3d-paws/3D-PAWS-Particle-SurgeAndWindGauge/src/output.cpp

/*
 * ======================================================================================================================
 *  output.cpp - OLED and Serial Console Fuctions
 * ======================================================================================================================
 */
#include "include/ssbits.h"
#include "include/support.h"
#include "include/main.h"
#include "include/output.h"

/*
 * ======================================================================================================================
 * Variables and Data Structures
 * =======================================================================================================================
 */

/*
 * ======================================================================================================================
 *  Serial Console Enable
 * ======================================================================================================================
 */
int SCE_PIN = D8;
bool SerialConsoleEnabled = false;  // Variable for serial monitor control

bool DisplayEnabled = true;
int  oled_type = 0;
char oled_lines[8][23];
Adafruit_SSD1306 display32(SCREEN_WIDTH, 32, &Wire, OLED_RESET);
Adafruit_SSD1306 display64(SCREEN_WIDTH, 64, &Wire, OLED_RESET);

/*
 * ======================================================================================================================
 * Fuction Definations
 * =======================================================================================================================
 */

/*
 * ======================================================================================================================
 * OLED_sleepDisplay()
 * ======================================================================================================================
 */
void OLED_sleepDisplay() {
  if (DisplayEnabled) {
    if (OLED32) {
      display32.ssd1306_command(SSD1306_DISPLAYOFF);
    }
    else {
      display64.ssd1306_command(SSD1306_DISPLAYOFF);
    }
  }
}

/*
 * ======================================================================================================================
 * OLED_wakeDisplay()
 * ======================================================================================================================
 */
void OLED_wakeDisplay() {
  if (DisplayEnabled) {
    if (OLED32) {
      display32.ssd1306_command(SSD1306_DISPLAYON);
    }
    else {
      display64.ssd1306_command(SSD1306_DISPLAYON);
    }
  }
}

/*
 * ======================================================================================================================
 * OLED_spin() 
 * ======================================================================================================================
 */
void OLED_spin() {
  static int spin=0;
    
  if (DisplayEnabled) {
    if (OLED32) {
      display32.setTextColor(WHITE, BLACK); // Draw 'inverse' text
      display32.setCursor(120,24);
      display32.print(" ");
      display32.setCursor(120,24); 
    }
    else {
      display64.setTextColor(WHITE, BLACK); // Draw 'inverse' text
      display64.setCursor(120,24);
      display64.print(" ");
      display64.setCursor(120,24);
      display64.setCursor(120,56);
      display64.print(" ");
      display64.setCursor(120,56);       
    } 
    switch (spin++) {
      case 0 : msgp = (char *) "|"; break;
      case 1 : msgp = (char *) "/"; break;
      case 2 : msgp = (char *) "-"; break;
      case 3 : msgp = (char *) "\\"; break;
    }
    if (OLED32) {
      display32.print(msgp);
      display32.display();
    }
    else {
      display64.print(msgp);
      display64.display();
    }
    spin %= 4;
  }
}


/*
 * ======================================================================================================================
 * OLED_update() -- Output oled in memory map to display
 * ======================================================================================================================
 */
void OLED_update() {  
  if (DisplayEnabled) {
    if (OLED32) {
      display32.clearDisplay();
      display32.setCursor(0,0);             // Start at top-left corner
      display32.print(oled_lines [0]);
      display32.setCursor(0,8);
      display32.print(oled_lines [1]);
      display32.setCursor(0,16);
      display32.print(oled_lines [2]);
      display32.setCursor(0,24);  
      display32.print(oled_lines [3]);
      display32.display();
    }
    else {
      display64.clearDisplay();
      display64.setCursor(0,0);             // Start at top-left corner
      display64.print(oled_lines [0]);
      display64.setCursor(0,8);
      display64.print(oled_lines [1]);
      display64.setCursor(0,16);
      display64.print(oled_lines [2]);
      display64.setCursor(0,24);  
      display64.print(oled_lines [3]);
      display64.setCursor(0,32);  
      display64.print(oled_lines [4]);
      display64.setCursor(0,40);  
      display64.print(oled_lines [5]);
      display64.setCursor(0,48);  
      display64.print(oled_lines [6]);
      display64.setCursor(0,56);  
      display64.print(oled_lines [7]);
      display64.display();
     
    }
  }
}

/*
 * ======================================================================================================================
 * OLED_write() 
 * ======================================================================================================================
 */
void OLED_write(const char *str) {
  int c, len, bottom_line = 3;
  
  if (DisplayEnabled) {
    // move lines up
    for (c=0; c<=21; c++) {
      oled_lines [0][c] = oled_lines [1][c];
      oled_lines [1][c] = oled_lines [2][c];
      oled_lines [2][c] = oled_lines [3][c];
      if (OLED64) {
        oled_lines [3][c] = oled_lines [4][c];
        oled_lines [4][c] = oled_lines [5][c];
        oled_lines [5][c] = oled_lines [6][c];  
        oled_lines [6][c] = oled_lines [7][c];  
        bottom_line = 7;          
      }
    }

    // check length on new output line string
    len = strlen (str);
    if (len>21) {
      len = 21;
    }
    for (c=0; c<=len; c++) {
      oled_lines [bottom_line][c] = *(str+c);
    }

    // Adding Padding
    for (;c<=21; c++) {
      oled_lines [bottom_line][c] = ' ';
    }
    oled_lines [bottom_line][22] = (char) NULL;
    
    OLED_update();
  }
}

/*
 * ======================================================================================================================
 * OLED_write_noscroll() -- keep lines 1-3 and output on line 4
 * ======================================================================================================================
 */
void OLED_write_noscroll(const char *str) {
  int c, len, bottom_line = 3;

  if (OLED64) {
    bottom_line = 7;
  }

  if (DisplayEnabled) {
    len = strlen (str);
    if (len>21) {
      len = 21;
    }
    
    for (c=0; c<=len; c++) {
      oled_lines [bottom_line][c] = *(str+c);
    }

    // Adding Padding
    for (;c<=21; c++) {
      oled_lines [bottom_line][c] = ' ';
    }
    oled_lines [bottom_line][22] = (char) NULL;
    
    OLED_update();
  }
}

/*
 * ======================================================================================================================
 * Serial_write() 
 * ======================================================================================================================
 */
void Serial_write(const char *str) {
  if (SerialConsoleEnabled) {
    Serial.println(str);
  }
}

/*
 * ======================================================================================================================
 * Serial_writeln() 
 * ======================================================================================================================
 */
void Serial_writeln(const char *str) {
  if (SerialConsoleEnabled) {
    Serial.println(str);
    Serial.flush();
  }
}

/*
 * ======================================================================================================================
 * Output()
 * ======================================================================================================================
 */
void Output(const char *str) {
  OLED_write(str);
  Serial_write(str);
}

/*
 * ======================================================================================================================
 * OutputNS() - Output with no scroll on oled
 * ======================================================================================================================
 */
void OutputNS(const char *str) {
  OLED_write_noscroll(str);
  Serial_write(str);
}

/*
 * ======================================================================================================================
 * OLED_initialize() -- Initialize oled if enabled
 * ======================================================================================================================
 */
void OLED_initialize() {
  if (DisplayEnabled) {
    if (I2C_Device_Exist (OLED32_I2C_ADDRESS)) {
      oled_type = OLED32_I2C_ADDRESS;
      display32.begin(SSD1306_SWITCHCAPVCC, OLED32_I2C_ADDRESS);
      display32.clearDisplay();
      display32.setTextSize(1); // Draw 2X-scale text
      display32.setTextColor(WHITE);
      display32.setCursor(0, 0);
      for (int r=0; r<4; r++) {
        oled_lines[r][0]=0;
      }
      OLED_write("OLED32:OK");
    }
    else if (I2C_Device_Exist (OLED64_I2C_ADDRESS)) {
      oled_type = OLED64_I2C_ADDRESS;
      display64.begin(SSD1306_SWITCHCAPVCC, OLED64_I2C_ADDRESS);
      display64.clearDisplay();
      display64.setTextSize(1); // Draw 2X-scale text
      display64.setTextColor(WHITE);
      display64.setCursor(0, 0);
      for (int r=0; r<8; r++) {
        oled_lines[r][0]=0;
      }
      OLED_write("OLED64:OK");
    }
    else {
      DisplayEnabled = false;
    }
  }
}

/*
 * ======================================================================================================================
 * Serial_Initialize() -
 * ======================================================================================================================
 */
void Serial_Initialize() {
  // serial console enable pin
  pinMode(SCE_PIN, INPUT_PULLUP);   // Internal pullup resistor biases the pin to supply voltage.
                                    // If jumper set to ground, we enable serial console (low = enable)
  if (digitalRead(SCE_PIN) == LOW) {
    SerialConsoleEnabled = true;
  }

  // There are libraries that print to Serial Console so we need to initialize no mater what the jumper is set to.
  Serial.begin(9600);
  delay(1000); // prevents usb driver crash on startup, do not omit this

  if (SerialConsoleEnabled) {
    // Wait for serial port to be available
    if (!Serial.isConnected()) {
      OLED_write("Wait4 Serial Console");
    }
    int countdown=60; // Wait N seconds for serial connection, then move on.
    while (!Serial.isConnected() && countdown) {
      HeartBeat(); // Provices 250ms delay
      Blink(1, 750);
      countdown--;
    }

    Serial_writeln(""); // Send carriage return and linefeed
    
    if (DisplayEnabled) {
      Serial_writeln ("OLED:Enabled");
    }
    else {
      Serial_writeln ("OLED:Disabled");
    }
    Output ("SC:Enabled");
  }
}

/*
 * ======================================================================================================================
 * Output_Initialize() -
 * ======================================================================================================================
 */
void Output_Initialize() {
  OLED_initialize();
  Output("SER:Init");
  Serial_Initialize();
  Output("SER:OK");
}
