3d-paws/3D-PAWS-Particle-SurgeAndWindGauge/src/info.cpp

/*
 * ======================================================================================================================
 *  info.cpp - Station Information Functions
 * ======================================================================================================================
 */
#include <Particle.h>
#include <SdFat.h>
#include <RTClib.h>

#include "include/ssbits.h"
#include "include/eeprom.h"
#include "include/cf.h"
#include "include/sensors_i2c_44_47.h"
#include "include/sensors.h"
#include "include/wrda.h"
#include "include/sdcard.h"
#include "include/output.h"
#include "include/support.h"
#include "include/time.h"
#include "include/ps.h"
#include "include/obs.h"
#include "include/main.h"
#include "include/info.h"

/*
 * ======================================================================================================================
 * INFO_Do() - Get and Send System Information to Particle Cloud
 * ======================================================================================================================
 */
bool INFO_Do() {
  char buf[256];
  const char *comma = "";
  time_t ts = Time.now();

  Output("INFO_DO()");

  SendSystemInformation = false;

  memset(buf, 0, sizeof(buf));        // holds string of found sensors 
  memset(msgbuf, 0, sizeof(msgbuf));  // hold the json formatted message we are building for sending.

  JSONBufferWriter writer(msgbuf, sizeof(msgbuf)-1);
  writer.beginObject();

  writer.name("devid").value(System.deviceID());
  writer.name("devos").value(System.version());
  writer.name("freemem").value(System.freeMemory());
  writer.name("uptime").value(System.uptime());

#if PLATFORM_ID == PLATFORM_ARGON
  writer.name("type").value("argon");
#endif
#if PLATFORM_ID == PLATFORM_BORON
  writer.name("board").value("boron");
#endif

  sprintf (Buffer32Bytes, "%d-%02d-%02dT%02d:%02d:%02d",
    Time.year(ts), Time.month(ts), Time.day(ts),
    Time.hour(ts), Time.minute(ts), Time.second(ts));
  writer.name("at").value(Buffer32Bytes);

  writer.name("ver").value(versioninfo);
  writer.name("hth").value((int) SystemStatusBits);

   // Reboot/Reset Reason and data
  sprintf (Buffer32Bytes,"%d-%d", (int) System.resetReason(), (int) System.resetReasonData());
  writer.name("rr").value(Buffer32Bytes);

  sprintf (Buffer32Bytes,"6m");
  writer.name("obsi").value(Buffer32Bytes);

  sprintf (Buffer32Bytes,"6m");
  writer.name("obsti").value(Buffer32Bytes);

  // Time 2 Next Transmit in Seconds
  // sprintf (Buffer32Bytes, "%ds", (int) ((obs_tx_interval * 60) - ((System.millis() - LastTransmitTime)/1000)));
  // writer.name("t2nt").value(Buffer32Bytes);

  // Daily Reboot Countdown Timer
  writer.name("drct").value(DailyRebootCountDownTimer);

  // Need 2 Send File
  if (SD.exists(SD_n2s_file)) {
    File fp = SD.open(SD_n2s_file, FILE_WRITE);
    if (fp) {
      writer.name("n2s").value(fp.size());
      fp.close();
    }
    else {
      writer.name("n2s").value(-1);
    }
  }
  else {
    writer.name("n2s").value("NF");
  }

#if PLATFORM_ID == PLATFORM_ARGON
  writer.name("ps").value((digitalRead(PWR)) ? "USB" : "BATTERY");
  writer.name("bv").value(analogRead(BATT) * 0.0011224); // Battery Voltage
  writer.name("bcs").value((digitalRead(PWR) && !digitalRead(CHG)) ? "CHARGING" : "!CHARGING"); // Battery Charger State
#endif

#if PLATFORM_ID == PLATFORM_BORON
  // Power Source
  const char *ps[] = {"UNKN", "VIN", "USB_HOST", "USB_ADAPTER", "USB_OTG", "BATTERY"};
  int sps = System.powerSource();
  if ((sps>=0) && (sps<=5)) {
    writer.name("ps").value(ps[sps]);
  }
  else {
    writer.name("ps").value(sps);
  }

  // Battery Charge State
  const char *bs[] = {"UNKN", "!CHARGING", "CHARGING", "CHARGED", "DISCHARGING", "FAULT", "MISSING"};
  int sbs = System.batteryState();
  if ((sbs>=0) && (sbs<=6)) {
    writer.name("bcs").value(bs[sbs]);     
  }
  else {
    writer.name("bcs").value(sbs);
  }
  writer.name("bpc").value(System.batteryCharge(), 1);   // Battery Percent Charge
#endif

#if PLATFORM_ID == PLATFORM_ARGON
  WiFiSignal sig = WiFi.RSSI();
  writer.name("wss").value(sig.getStrength(), 4);
  writer.name("wsq").value(sig.getQuality(), 4);
  byte mac[6];
  WiFi.macAddress(mac);
  sprintf (Buffer32Bytes, "%02x:%02x:%02x:%02x:%02x:%02x", mac[0], mac[1], mac[2], mac[3], mac[4], mac[5]);
  writer.name("mac").value(Buffer32Bytes);
  writer.name("ip").value(WiFi.localIP().toString().c_str());
  writer.name("mask").value(WiFi.subnetMask().toString().c_str());
  writer.name("gateway").value(WiFi.gatewayIP().toString().c_str());
  writer.name("dns").value(WiFi.dnsServerIP().toString().c_str());
  writer.name("dhcps").value(WiFi.dhcpServerIP().toString().c_str());
  writer.name("ssid").value(WiFi.SSID());
  WiFi.BSSID(mac);
  sprintf (Buffer32Bytes, "%02x:%02x:%02x:%02x:%02x:%02x", mac[0], mac[1], mac[2], mac[3], mac[4], mac[5]);
  writer.name("bssid").value(Buffer32Bytes);
#endif

#if PLATFORM_ID == PLATFORM_BORON
  CellularSignal sig = Cellular.RSSI();
  writer.name("css").value(sig.getStrength(), 4);
  writer.name("csq").value(sig.getQuality(), 4);
  writer.name("imsi").value(imsi); // International Mobile Subscriber Identity

  SimType simType = Cellular.getActiveSim();
  if (simType == INTERNAL_SIM) {
    writer.name("actsim").value("INTERNAL");
  } else if (simType == EXTERNAL_SIM) {
    writer.name("actsim").value("EXTERNAL");
  } else {
    writer.name("actsim").value("ERR");
  }
#endif

  // OP1 pin is set
  if (dg_adjustment == 1.25) {
    writer.name("op1").value("DIST 5M(a4)");
  }
  else {
    writer.name("op1").value("DIST 10M(a4)");
  }

  // OP2 pin is set
  if (OP2_State == OP2_STATE_RAW){
    writer.name("op2").value("RAW");
  }
  else if (OP2_State == OP2_STATE_VOLTAIC){
    writer.name("op2").value("VBV(A5)");
  }
  else {
    writer.name("op2").value("NS(A5)"); // Not Set
  }

  // Station Elevation
  writer.name("elev").value(cf_elevation);



  // Sensors
  buf[0] = '\0';
  if (BMX_1_exists) {
    sprintf (buf+strlen(buf), "%sBMX1(%s)", comma, bmxtype[BMX_1_type]);
    comma=",";
  }
  if (BMX_2_exists) {
    sprintf (buf+strlen(buf), "%sBMX2(%s)", comma, bmxtype[BMX_2_type]);
    comma=",";
  }

  // Add 0x44-)x47 sensors to the list
  sensor_i2c_44_47_info(buf, 256, comma);

  if (MCP_1_exists) {
    sprintf (buf+strlen(buf), "%sMCP1", comma);
    comma=",";
  }
  if (MCP_2_exists) {
    sprintf (buf+strlen(buf), "%sMCP2", comma);
    comma=",";
  }
  if (SI1145_exists) {
    sprintf (buf+strlen(buf), "%sSI", comma);
    comma=",";
  }
  if (VEML7700_exists) {
    sprintf (buf+strlen(buf), "%sVEML", comma);
    comma=",";
  }
  if (DoWind) { // Wind Sensor
    GetPinName(ANEMOMETER_IRQ_PIN, Buffer32Bytes);
    sprintf (buf+strlen(buf), "%sWS(%s)", comma, Buffer32Bytes);
    comma=",";
  }
  if (AS5600_exists) {
    sprintf (buf+strlen(buf), "%sAS5600", comma);
    comma=",";
  }
  if (HI_exists) {
    sprintf (buf+strlen(buf), "%sHI", comma);
    comma=",";
  }
  if (MSLP_exists) {
    sprintf (buf+strlen(buf), "%sMSLP", comma);
    comma=",";  
  }
  writer.name("sensors").value(buf);

    // RTC
  if (RTC_exists) {
    writer.name("rtc").value("OK");
  }
  else {
    writer.name("rtc").value("NF");
  }

  // Oled Display
  if (oled_type) {
    writer.name("oled").value(OLED32 ? "32" : "64");
  }
  else {
    writer.name("oled").value("NF");
  }
  writer.name("scepin").value((digitalRead(SCE_PIN)) ? "DISABLED" : "ENABLED");
  writer.name("sce").value((SerialConsoleEnabled) ? "TRUE" : "FALSE");

  writer.endObject();

  // Done profiling system

  // Update INFO.TXT file
  if (SD_exists) {
    File fp = SD.open(SD_INFO_FILE, FILE_WRITE | O_TRUNC); 
    if (fp) {
      fp.println(msgbuf);
      fp.close();
      SystemStatusBits &= ~SSB_SD;  // Turn Off Bit
      // Output ("INFO Logged to SD");
    }
    else {
      SystemStatusBits |= SSB_SD;  // Turn On Bit - Note this will be reported on next observation
      Output ("SD:Open(Info)ERR");
    }
  }

  if (Particle_Publish((char *) "INFO")) {
    Serial_write (msgbuf);
    sprintf (Buffer32Bytes, "INFO->PUB OK[%d]", strlen(msgbuf)+1);
    Output(Buffer32Bytes);
    return(true);
  }
  else {
    sprintf (Buffer32Bytes, "INFO->PUB ERR");
    Output(Buffer32Bytes);
    return(false);
  }
}
