3d-paws/3D-PAWS-Particle-SurgeAndWindGauge/src/statmon.cpp

/*
 * ======================================================================================================================
 * statmon.cpp - Station Monitor - When Jumper Set Main Loop runs StationMonitor()
 * ======================================================================================================================
 */
#include <Particle.h>
#include <RTClib.h>

#include "include/ssbits.h"
#include "include/sensors_i2c_44_47.h"
#include "include/sensors.h"
#include "include/wrda.h"
#include "include/cf.h"
#include "include/output.h"
#include "include/support.h"
#include "include/time.h"
#include "include/main.h"
#include "include/statmon.h"

/*
 * ======================================================================================================================
 * Variables and Data Structures
 * =======================================================================================================================
 */

/*
 * ======================================================================================================================
 * Fuction Definations
 * =======================================================================================================================
 */

/*
 * ======================================================================================================================
 * StationMonitor() - On OLED display station information
 * ======================================================================================================================
 */
void StationMonitor() {
  static int cycle = 0;
  static int count = 0;
  int r, c, len;

  // Clear display with spaces
  for (r=0; r<4; r++) {
    for (c=0; c<22; c++) {
      oled_lines [r][c] = ' ';
    }
    oled_lines [r][c] = (char) NULL;
  }
  
  // =================================================================
  // Line 0 of OLED
  // =================================================================
  stc_timestamp();
  len = (strlen (timestamp) > 21) ? 21 : strlen (timestamp);
  for (c=0; c<=len; c++) oled_lines [0][c] = *(timestamp+c);
  Serial_writeln (timestamp);

  // =================================================================
  // Line 1 of OLED Distance Median & Distance Raw
  // =================================================================
  memset(msgbuf, 0, sizeof(msgbuf));

  float distance = DistanceGauge_SimpleMedian() * dg_adjustment; // Pins are 12bit resolution 

  sprintf (msgbuf+strlen(msgbuf), "DM:%d.%02d DR:%d %s", 
    (int)distance, (int)(distance*100)%100, (int) analogRead(DISTANCEGAUGE),
    (dg_adjustment == 1.25) ? "5M" : "10M");

  len = (strlen (msgbuf) > 21) ? 21 : strlen (msgbuf);
  for (c=0; c<=len; c++) oled_lines [1][c] = *(msgbuf+c);
  Serial_writeln (msgbuf);

  // =================================================================
  // Line 2 of OLED Wind Direction and Wind Speed
  // =================================================================
  memset(msgbuf, 0, sizeof(msgbuf));

  if (AS5600_exists) {
    float ws = Wind_SpeedAverage();
    sprintf (msgbuf, "WD:%3d WS:%d.%02d", 
      Wind_SampleDirection(), (int)ws, (int)(ws*100)%100);
  }
  else {
    sprintf (msgbuf, "WD:NF  WS:NF");
  }
  
  len = (strlen (msgbuf) > 21) ? 21 : strlen (msgbuf);
  for (c=0; c<=len; c++) oled_lines [2][c] = *(msgbuf+c);
  Serial_writeln (msgbuf);
  
  // =================================================================
  // Line 3 of OLED Cycle between multiple sensors
  // =================================================================
  if (cycle == 0) {
    if (BMX_1_exists) {
      float p,t,h;
      bmx1_read(p, t, h);
      sprintf (msgbuf, "B1 %.2f %.2f %.2f", p,t,h);
    }
    else {
      sprintf (msgbuf, "B1 NF");
    }
  }

  if (cycle == 1) {
    if (BMX_2_exists) {
      float p,t,h;
      bmx2_read(p, t, h);
      sprintf (msgbuf, "B2 %.2f %.2f %.2f", p,t,h);
    }
    else {
      sprintf (msgbuf, "B2 NF");
    }
  }

  if (cycle == 2) {
    memset(msgbuf, 0, sizeof(msgbuf));
      
    if (MCP_1_exists) {
      float mcp_temp = mcp1.readTempC();   
      sprintf (msgbuf, "MCP1 T%d.%02d", (int)mcp_temp, (int)(mcp_temp*100)%100);
    }
    else {
      sprintf (msgbuf, "MCP1 NF");
    }
  }

  if (cycle == 3) {
    if (MCP_2_exists) {
      float mcp_temp = mcp2.readTempC();   
      sprintf (msgbuf, "MCP2 T%d.%02d", (int)mcp_temp, (int)(mcp_temp*100)%100);
    }
    else {
      sprintf (msgbuf, "MCP2 NF");
    }
  }

  if (cycle == 4) {
   sensor_i2c_44_47_statmon(0, Buffer32Bytes);
   sprintf (msgbuf, "%s", Buffer32Bytes);
  }
  if (cycle == 5) {
   sensor_i2c_44_47_statmon(1, Buffer32Bytes);
   sprintf (msgbuf, "%s", Buffer32Bytes);
  }
  if (cycle == 6) {
   sensor_i2c_44_47_statmon(2, Buffer32Bytes);
   sprintf (msgbuf, "%s", Buffer32Bytes);
  }
  if (cycle == 7) {
   sensor_i2c_44_47_statmon(3, Buffer32Bytes);
   sprintf (msgbuf, "%s", Buffer32Bytes);
  }

  if (cycle == 8) {   
    if (HTU21DF_exists) {
      float htu_humid = htu.readHumidity();
      float htu_temp = htu.readTemperature();

      sprintf (msgbuf, "HTU H:%02d.%02d T:%02d.%02d", 
        (int)htu_humid, (int)(htu_humid*100)%100, 
        (int)htu_temp, (int)(htu_temp*100)%100);
    }
    else {
      sprintf (msgbuf, "HTU NF"); 
    } 
  }

  if (cycle == 9) {   
    if (VEML7700_exists) {
      float lux = veml.readLux(VEML_LUX_AUTO);
      lux = (isnan(lux)) ? 0.0 : lux;
        sprintf (msgbuf, "LX L%02d.%1d", (int)lux, (int)(lux*10)%10);
    }
    else {
      sprintf (msgbuf, "LX NF");
    }
  }

  if (cycle == 10) {
    if (SI1145_exists) {
      float si_vis = uv.readVisible();
      float si_ir = uv.readIR();
      float si_uv = uv.readUV()/100.0;
      sprintf (msgbuf, "SI V%d.%02d I%d.%02d U%d.%02d", 
        (int)si_vis, (int)(si_vis*100)%100,
        (int)si_ir, (int)(si_ir*100)%100,
        (int)si_uv, (int)(si_uv*100)%100);
    }
    else {
      sprintf (msgbuf, "SI NF");
    }
  }

  if (cycle == 11) {
    memset(msgbuf, 0, sizeof(msgbuf));

#if PLATFORM_ID == PLATFORM_ARGON
    WiFiSignal sig = WiFi.RSSI();
    float SignalStrength = sig.getStrength();
    int BatteryState = 0;
#else
    CellularSignal sig = Cellular.RSSI();
    float SignalStrength = sig.getStrength();
#endif
    sprintf (msgbuf+strlen(msgbuf), "CSS:%d.%02d HTH:%X",
      (int)SignalStrength, (int)(SignalStrength*100)%100,
      (int)SystemStatusBits); 
  }

  len = (strlen (msgbuf) > 21) ? 21 : strlen (msgbuf);
  for (c=0; c<=len; c++) oled_lines [3][c] = *(msgbuf+c);
  Serial_writeln (msgbuf);

  // Give the use some time to read line 3 before changing
  if (count++ >= 5) {
    cycle = (cycle+1) % 12; // << +1
    count = 0;
  }
  
  OLED_update();
}
