3d-paws/3D-PAWS-Particle-SurgeAndWindGauge/src/include/obs.h

/*
 * ======================================================================================================================
 *  obs.h - Observation Definations
 * ====================================================================================================================== 
 */

// Extern variables
extern float bmx_1_pressure;

// Function prototypes
bool Particle_Publish(char *EventName);
void OBS_Do();
