3d-paws/3D-PAWS-Particle-SurgeAndWindGauge/src/include/cf.h

/*
 * ======================================================================================================================
 *  cf.h - Configuration File Definations
 * ======================================================================================================================
 */

/* 
 * ======================================================================================================================
#
# CONFIG.TXT
#
# Line Length is limited to 63 characters
#12345678901234567890123456789012345678901234567890123456789012

* ======================================================================================================================
*/

/*
 * ======================================================================================================================
 *  Define Global Configuration File Variables
 * ======================================================================================================================
 */
#define CF_NAME           "CONFIG.TXT"
#define KEY_MAX_LENGTH    30                // Config File Key Length
#define VALUE_MAX_LENGTH  30                // Config File Value Length
#define LINE_MAX_LENGTH   VALUE_MAX_LENGTH+KEY_MAX_LENGTH+3   // =, CR, LF 

// Extern variables
extern int cf_elevation;

// Function prototypes
void SD_ReadConfigFile();
void SD_ReadElevationFile();
