3d-paws/3D-PAWS-Particle-SurgeAndWindGauge/src/include/info.h

/*
 * ======================================================================================================================
 *  info.h - Station Information Definations
 * ======================================================================================================================
 */

// Extern variables

// Function prototypes
bool INFO_Do();
