3d-paws/3D-PAWS-Particle-SurgeAndWindGauge/src/include/statmon.h

/*
 * ======================================================================================================================
 *  statmon.h - Station Monitor Definations
 * ======================================================================================================================
 */

// Extern variables

// Function prototypes
void StationMonitor();
